slash-builder/hw-2015-dial-panel/cad/step/03-screen-trim.step

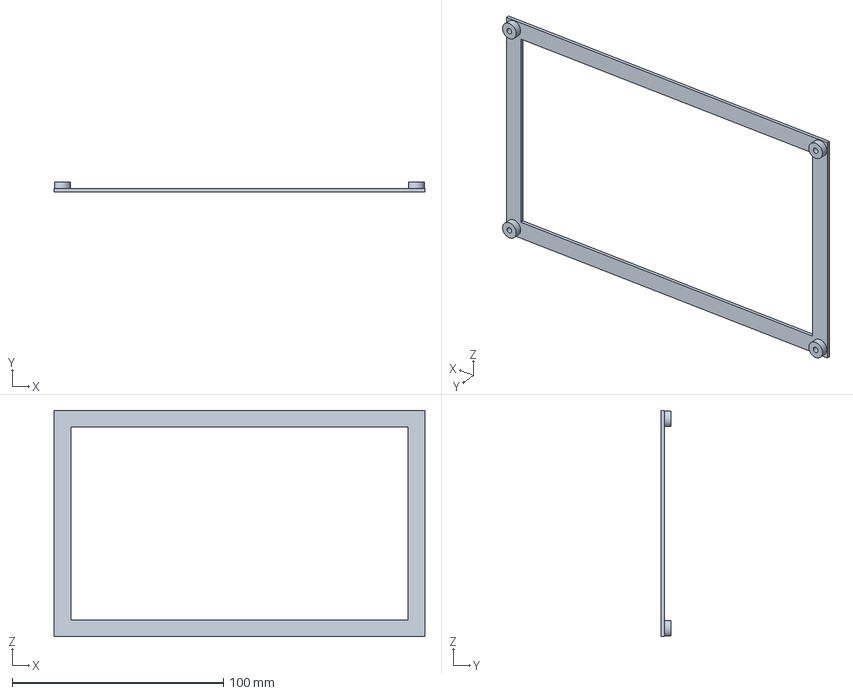
[picture p16: CAD file, 2026-09-25]
cad/step/03-screen-trim.step
175.8 x 4.60 x 107.3 mm
