slash-builder/hw-2015-dial-panel/stl/common/05-band-diffuser.stl

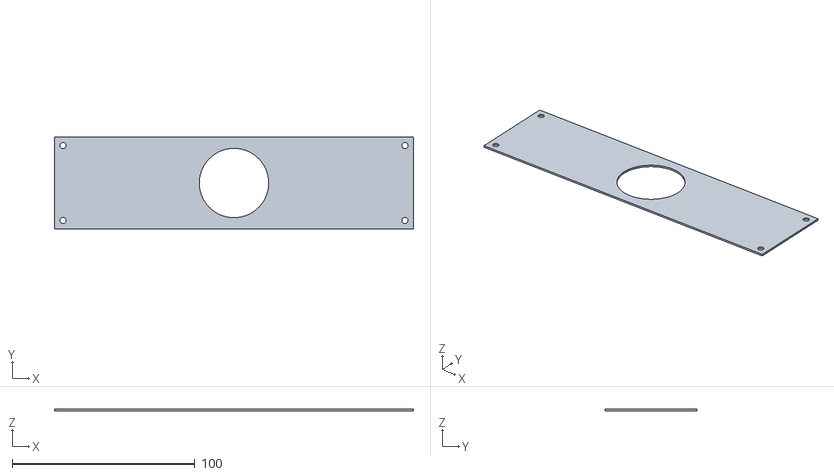
[picture p17: CAD file, 2026-09-24]
stl/common/05-band-diffuser.stl
196.7 x 50.4 x 1.00
