slash-builder/hw-2015-dial-panel/cad/coupons/C2-band-insert-ignition-band-mount.step

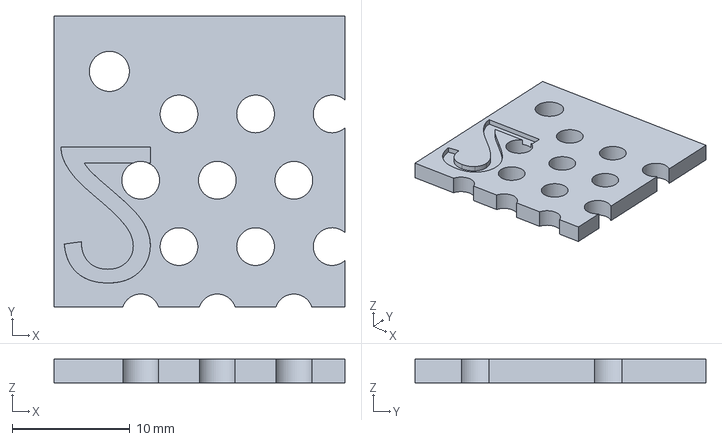
[picture p18: CAD file, 2026-09-25]
cad/coupons/C2-band-insert-ignition-band-mount.step
24.7 x 24.7 x 2.00 mm
