slash-builder/hw-2015-dial-panel/cad/step/12-cleat-receiver-rail.step

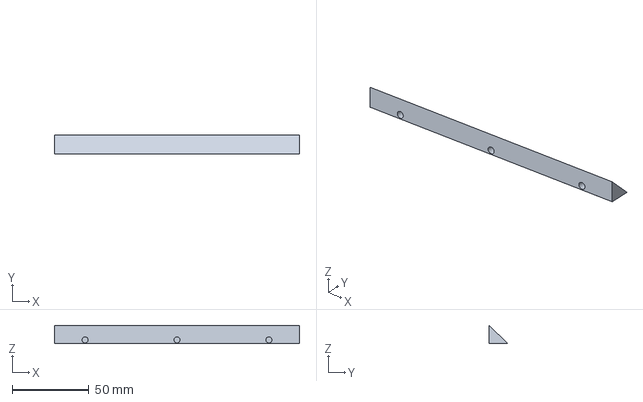
[picture p19: CAD file, 2026-09-25]
cad/step/12-cleat-receiver-rail.step
160.0 x 12.5 x 12.0 mm
