slash-builder/hw-2015-dial-panel/stl/common/02a-back-shell-screen.stl

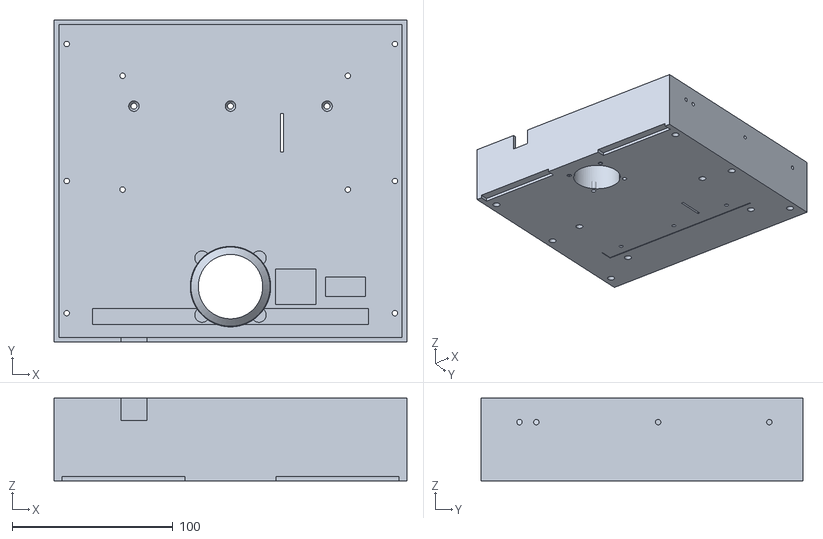
[picture p20: CAD file, 2026-09-23]
stl/common/02a-back-shell-screen.stl
219.3 x 200.2 x 51.6
