slash-builder/hw-2015-dial-panel/cad/coupons/C1-face-plate-screen-band-mount.step

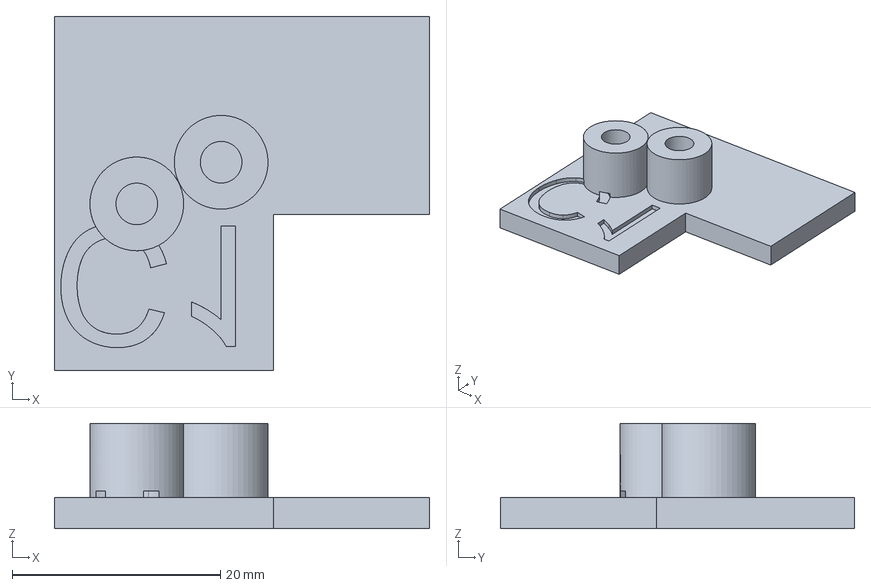
[picture p21: CAD file, 2026-09-25]
cad/coupons/C1-face-plate-screen-band-mount.step
36.0 x 34.0 x 10.1 mm
