slash-builder/hw-2015-dial-panel/cad/coupons/B1-back-shell-column-seam.step

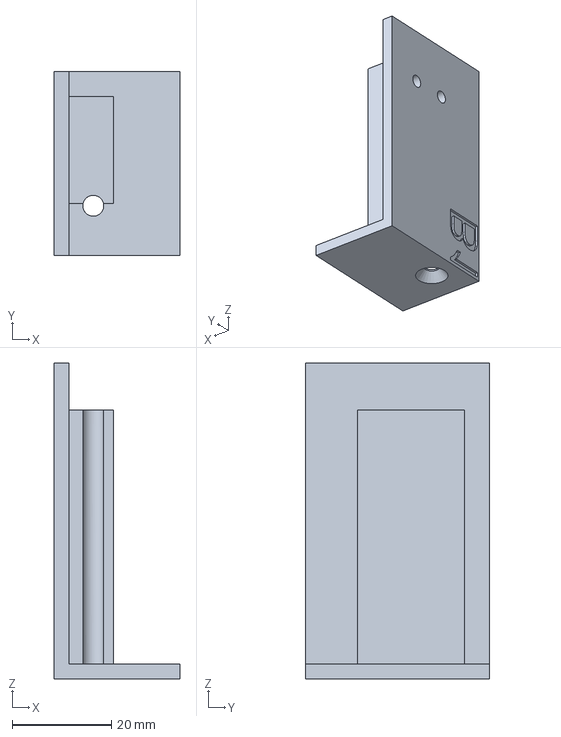
[picture p22: CAD file, 2026-09-25]
cad/coupons/B1-back-shell-column-seam.step
25.3 x 37.0 x 63.6 mm
