slash-builder/hw-2015-dial-panel/cad/step/11-wall-cleat.step

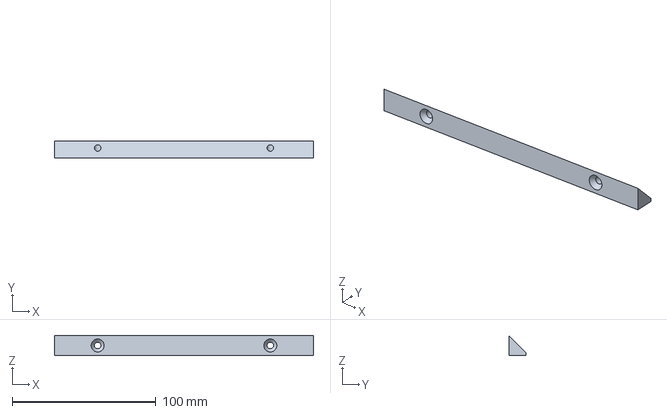
[picture p23: CAD file, 2026-09-25]
cad/step/11-wall-cleat.step
180.0 x 11.9 x 13.9 mm
