slash-builder/hw-2015-dial-panel/stl/common/07-gold-tab.stl

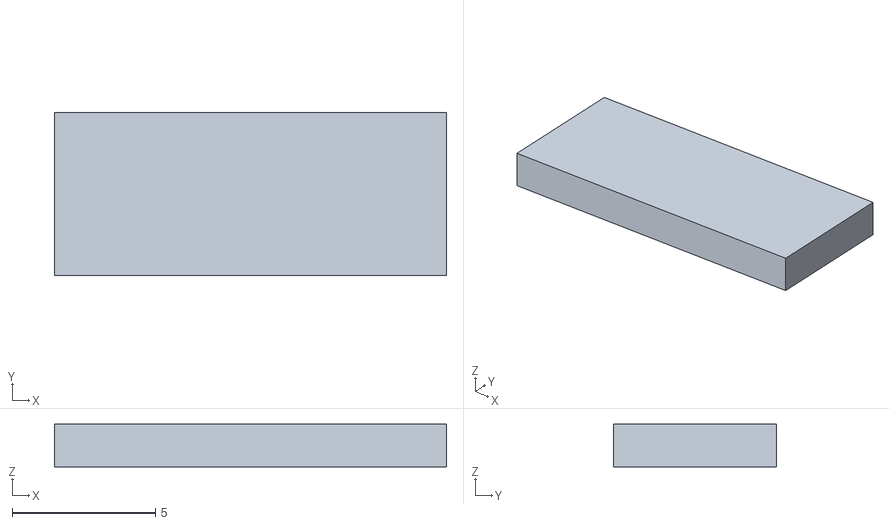
[picture p24: CAD file, 2026-09-22]
stl/common/07-gold-tab.stl
13.7 x 5.70 x 1.50
