slash-builder/hw-2015-dial-panel/software/dial-sim/src/font.rs

//! A 5×7 bitmap font, built in.
//!
//! The harness needs to draw a handful of words, and depending on a font file
//! means depending on where that file lives on somebody else's machine. Seven
//! bytes a glyph avoids the whole question, and the result reads like an
//! instrument panel, which suits the device.

/// Rows top to bottom; the low five bits of each byte, leftmost pixel high.
pub fn glyph(c: char) -> [u8; 7] {
    match c.to_ascii_uppercase() {
        '0' => [0x0E, 0x11, 0x13, 0x15, 0x19, 0x11, 0x0E],
        '1' => [0x04, 0x0C, 0x04, 0x04, 0x04, 0x04, 0x0E],
        '2' => [0x0E, 0x11, 0x01, 0x02, 0x04, 0x08, 0x1F],
        '3' => [0x1F, 0x02, 0x04, 0x02, 0x01, 0x11, 0x0E],
        '4' => [0x02, 0x06, 0x0A, 0x12, 0x1F, 0x02, 0x02],
        '5' => [0x1F, 0x10, 0x1E, 0x01, 0x01, 0x11, 0x0E],
        '6' => [0x06, 0x08, 0x10, 0x1E, 0x11, 0x11, 0x0E],
        '7' => [0x1F, 0x01, 0x02, 0x04, 0x08, 0x08, 0x08],
        '8' => [0x0E, 0x11, 0x11, 0x0E, 0x11, 0x11, 0x0E],
        '9' => [0x0E, 0x11, 0x11, 0x0F, 0x01, 0x02, 0x0C],

        'A' => [0x0E, 0x11, 0x11, 0x1F, 0x11, 0x11, 0x11],
        'B' => [0x1E, 0x11, 0x11, 0x1E, 0x11, 0x11, 0x1E],
        'C' => [0x0E, 0x11, 0x10, 0x10, 0x10, 0x11, 0x0E],
        'D' => [0x1E, 0x11, 0x11, 0x11, 0x11, 0x11, 0x1E],
        'E' => [0x1F, 0x10, 0x10, 0x1E, 0x10, 0x10, 0x1F],
        'F' => [0x1F, 0x10, 0x10, 0x1E, 0x10, 0x10, 0x10],
        'G' => [0x0E, 0x11, 0x10, 0x17, 0x11, 0x11, 0x0F],
        'H' => [0x11, 0x11, 0x11, 0x1F, 0x11, 0x11, 0x11],
        'I' => [0x0E, 0x04, 0x04, 0x04, 0x04, 0x04, 0x0E],
        'J' => [0x07, 0x02, 0x02, 0x02, 0x02, 0x12, 0x0C],
        'K' => [0x11, 0x12, 0x14, 0x18, 0x14, 0x12, 0x11],
        'L' => [0x10, 0x10, 0x10, 0x10, 0x10, 0x10, 0x1F],
        'M' => [0x11, 0x1B, 0x15, 0x15, 0x11, 0x11, 0x11],
        'N' => [0x11, 0x11, 0x19, 0x15, 0x13, 0x11, 0x11],
        'O' => [0x0E, 0x11, 0x11, 0x11, 0x11, 0x11, 0x0E],
        'P' => [0x1E, 0x11, 0x11, 0x1E, 0x10, 0x10, 0x10],
        'Q' => [0x0E, 0x11, 0x11, 0x11, 0x15, 0x12, 0x0D],
        'R' => [0x1E, 0x11, 0x11, 0x1E, 0x14, 0x12, 0x11],
        'S' => [0x0F, 0x10, 0x10, 0x0E, 0x01, 0x01, 0x1E],
        'T' => [0x1F, 0x04, 0x04, 0x04, 0x04, 0x04, 0x04],
        'U' => [0x11, 0x11, 0x11, 0x11, 0x11, 0x11, 0x0E],
        'V' => [0x11, 0x11, 0x11, 0x11, 0x11, 0x0A, 0x04],
        'W' => [0x11, 0x11, 0x11, 0x15, 0x15, 0x1B, 0x11],
        'X' => [0x11, 0x11, 0x0A, 0x04, 0x0A, 0x11, 0x11],
        'Y' => [0x11, 0x11, 0x0A, 0x04, 0x04, 0x04, 0x04],
        'Z' => [0x1F, 0x01, 0x02, 0x04, 0x08, 0x10, 0x1F],

        '%' => [0x19, 0x1A, 0x02, 0x04, 0x08, 0x0B, 0x13],
        '-' => [0x00, 0x00, 0x00, 0x1F, 0x00, 0x00, 0x00],
        '+' => [0x00, 0x04, 0x04, 0x1F, 0x04, 0x04, 0x00],
        '.' => [0x00, 0x00, 0x00, 0x00, 0x00, 0x0C, 0x0C],
        ',' => [0x00, 0x00, 0x00, 0x00, 0x0C, 0x0C, 0x08],
        ':' => [0x00, 0x0C, 0x0C, 0x00, 0x0C, 0x0C, 0x00],
        '/' => [0x01, 0x02, 0x02, 0x04, 0x08, 0x08, 0x10],
        '°' => [0x0E, 0x0A, 0x0E, 0x00, 0x00, 0x00, 0x00],
        '·' => [0x00, 0x00, 0x00, 0x0C, 0x0C, 0x00, 0x00],
        '(' => [0x02, 0x04, 0x08, 0x08, 0x08, 0x04, 0x02],
        ')' => [0x08, 0x04, 0x02, 0x02, 0x02, 0x04, 0x08],

        _ => [0; 7], // space, and anything this font does not carry
    }
}

pub const GLYPH_W: usize = 5;
pub const GLYPH_H: usize = 7;

/// Width in pixels of `text` at `scale`, including inter-character gaps.
pub fn text_width(text: &str, scale: usize, tracking: usize) -> usize {
    let n = text.chars().count();
    if n == 0 {
        return 0;
    }
    n * GLYPH_W * scale + (n - 1) * tracking
}

/// Height in pixels of a line at `scale`.
pub fn text_height(scale: usize) -> usize {
    GLYPH_H * scale
}
